EduKreiman/Controladora-Termica-Programable-V0/Version03/hardware/ACS712 current-sensor.png

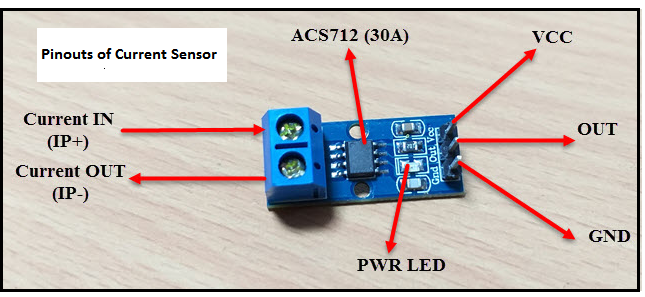
Version03/hardware/ACS712 current-sensor.png
