EduKreiman/Controladora-Termica-Programable-V0/Version03/hardware/CTP-equipo .jpg

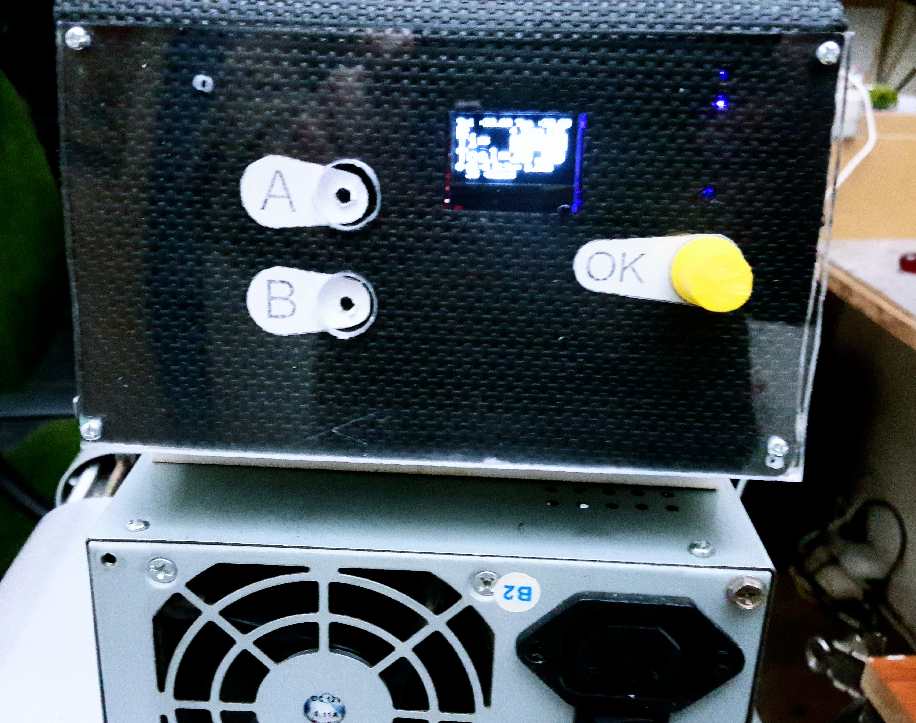
Version03/hardware/CTP-equipo .jpg
