EduKreiman/Controladora-Termica-Programable-V0/Version03/hardware/display oled 1330 lado cobre.jpg

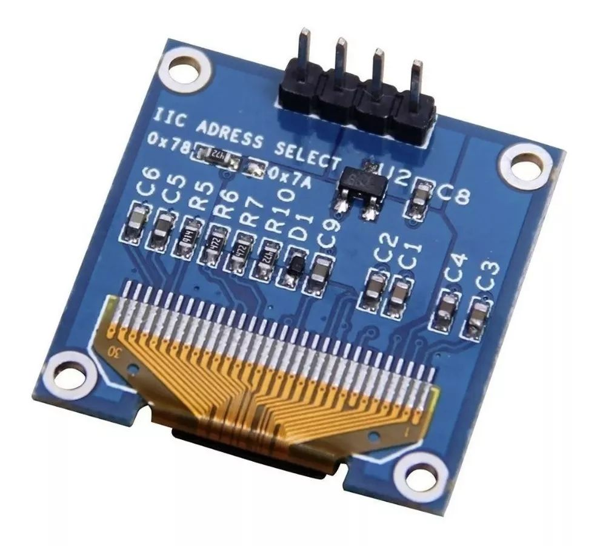
Version03/hardware/display oled 1330 lado cobre.jpg
